DL8UG/HORCHPOSTEN-ESP32-CW-BINAURAL/firmware/main/pitch.h

/*
 * Auto pitch: find the strongest CW tone in a block of audio.
 */
#pragma once

#include <stdbool.h>
#include <stddef.h>

#define PITCH_CAPTURE_MS  300

/*
 * Search fmin..fmax Hz (sample rate fs) for the strongest tone.
 * Returns true and the frequency in *hz if the peak stands at least
 * 14 dB above the noise beside it (20..60 Hz away), and false if the
 * strongest tone lies outside fmin..fmax.
 * The buffer is overwritten (windowed).
 */
bool pitch_detect(float *buf, size_t n, int fs, int fmin, int fmax, float *hz);
